Arush-Reddy/DoorCam/firmware/doorbell_cam/credentials.sample.h

#pragma once

// Template Wi-Fi and Server Configuration
// Copy this file to 'credentials.h' and fill in your Wi-Fi and host server IP
const char* ssid = "YOUR_WIFI_SSID";
const char* password = "YOUR_WIFI_PASSWORD";
const char* serverHost = "192.168.0.4"; // IP of machine running doorbell_server.py
const int serverPort = 5000;
